boreq/vivarium/vivarium_assistant/src/domain/outputs.rs

use super::{InputPin, OutputPin, OutputPinState, PinNumber, GPIO};
use crate::errors::Result;
use anyhow::anyhow;
use chrono::TimeDelta;
use chrono::{DateTime, Local, NaiveTime, Utc};
use log::info;
use std::fmt::Display;
use std::time::Duration;

pub trait CurrentTimeProvider {
    fn now(&self) -> DateTime<Utc>;
}

#[derive(Copy, Debug, Clone, PartialEq)]
pub struct ScheduledActivation {
    when: NaiveTime,
    for_seconds: u32,
}

impl ScheduledActivation {
    const SECONDS_IN_AN_IMAGINARY_DAY: u32 = 24 * 60 * 60;

    pub fn new(when: NaiveTime, for_seconds: u32) -> Result<Self> {
        if for_seconds == 0 {
            return Err(anyhow!("activating for 0 seconds is nonsense"));
        }

        if for_seconds > ScheduledActivation::SECONDS_IN_AN_IMAGINARY_DAY {
            return Err(anyhow!(format!(
                "since this type effectively represents durations on an imaginary clock face this
                time the day really is up to {} seconds long and it isn't just the programmer's
                delusion; the provided for_seconds exceeds that",
                ScheduledActivation::SECONDS_IN_AN_IMAGINARY_DAY
            )));
        }

        Ok(Self { when, for_seconds })
    }

    pub fn overlaps(&self, other: &Self) -> bool {
        if self.has_inside(&other.when) {
            return true;
        }
        if self.has_inside(&other.end()) {
            return true;
        }
        if other.has_inside(&self.end()) {
            return true;
        }

        false
    }

    pub fn has_inside(&self, time: &NaiveTime) -> bool {
        let start = self.when;
        let end = self.end();

        if start == end {
            return true;
        }

        let jumps_over_midnight = end < start;
        if jumps_over_midnight {
            time >= &start || time <= &end
        } else {
            time >= &start && time <= &end
        }
    }

    pub fn repeat(&self, start_every_seconds: u32, times: u32) -> Result<Vec<ScheduledActivation>> {
        if start_every_seconds == 0 {
            return Err(anyhow!("repeating every zero seconds makes no sense"));
        }

        if start_every_seconds <= self.for_seconds {
            return Err(anyhow!("repeating more often than or just as often as for_seconds makes no sense, the results will overlap"));
        }

        if times <= 1 {
            return Err(anyhow!(
                "repeating less than two times makes no sense, just use the existing activation"
            ));
        }

        let mut result = vec![];
        let start_every = Duration::from_secs(start_every_seconds.into());
        for i in 0..times {
            let jump = start_every * i;
            if jump.as_secs() >= ScheduledActivation::SECONDS_IN_AN_IMAGINARY_DAY.into() {
                return Err(anyhow!(
                    "there is no way we meant to jump by more than a whole day or a whole day when repeating"
                ));
            }
            let when = self.when + jump;
            let when_jumps_over_midnight = when < self.when;
            if when_jumps_over_midnight {
                return Err(anyhow!(
                    "I find it highly suspicious that we jumped over midnight when repeating, I suspect we didn't want this to happen"
                ));
            }

            let activation = ScheduledActivation::new(when, self.for_seconds)?;
            result.push(activation);
        }
        Ok(result)
    }

    fn end(&self) -> NaiveTime {
        self.when + TimeDelta::seconds(self.for_seconds as i64)
    }
}

#[derive(Debug, Clone, PartialEq)]
pub struct ScheduledActivations {
    activations: Vec<ScheduledActivation>,
}

impl ScheduledActivations {
    pub fn new(activations: &[ScheduledActivation]) -> Result<Self> {
        let mut v = vec![];
        for (i, a) in activations.iter().enumerate() {
            for (j, b) in activations.iter().enumerate() {
                if i != j && a.overlaps(b) {
                    return Err(anyhow!("activations can't overlap"));
                }
            }
            v.push(*a);
        }

        Ok(ScheduledActivations { activations: v })
    }

    pub fn has_inside(&self, time: &NaiveTime) -> bool {
        for activation in &self.activations {
            if activation.has_inside(time) {
                return true;
            }
        }
        false
    }
}

#[derive(Debug, Clone, Hash, Eq, PartialEq)]
pub struct OutputName {
    name: String,
}

impl OutputName {
    pub fn new(name: impl Into<String>) -> Result<Self> {
        let name = name.into();
        if name.is_empty() {
            return Err(anyhow!("output name can't be empty"));
        }
        Ok(Self { name })
    }

    pub fn name(&self) -> &str {
        &self.name
    }
}

impl Display for OutputName {
    fn fmt(&self, f: &mut std::fmt::Formatter<'_>) -> std::fmt::Result {
        write!(f, "{}", self.name)
    }
}

#[derive(Debug, Clone, PartialEq)]
pub struct OutputDefinition {
    name: OutputName,
    pin: PinNumber,
    activations: ScheduledActivations,
}

impl OutputDefinition {
    pub fn new(name: OutputName, pin: PinNumber, activations: ScheduledActivations) -> Self {
        Self {
            name,
            pin,
            activations,
        }
    }
}

#[derive(Debug, Clone, PartialEq)]
pub struct OutputDefinitions {
    outputs: Vec<OutputDefinition>,
}

impl OutputDefinitions {
    pub fn new(outputs: &[OutputDefinition]) -> Result<Self> {
        let mut v = vec![];
        for (i, a) in outputs.iter().enumerate() {
            for (j, b) in outputs.iter().enumerate() {
                if i == j {
                    continue;
                }

                if a.name == b.name {
                    return Err(anyhow!("identical output names"));
                }

                if a.pin == b.pin {
                    return Err(anyhow!("duplicate pin numbers"));
                }
            }
            v.push(a.clone());
        }

        Ok(Self { outputs: v })
    }

    pub fn outputs(&self) -> &[OutputDefinition] {
        &self.outputs
    }
}

pub struct Controller<OP: OutputPin, CTP: CurrentTimeProvider> {
    outputs: Vec<ControlledOutput<OP>>,
    current_time_provider: CTP,
}

impl<OP: OutputPin, CTP: CurrentTimeProvider> Controller<OP, CTP> {
    pub fn new<IP: InputPin, GP: GPIO<OP, IP>>(
        outputs: &OutputDefinitions,
        gpio: GP,
        current_time_provider: CTP,
    ) -> Result<Controller<OP, CTP>> {
        let outputs_with_pin: Result<Vec<ControlledOutput<OP>>> = outputs
            .outputs()
            .iter()
            .map(|v| {
                Ok(ControlledOutput {
                    definition: v.clone(),
                    overrides: vec![],
                    pin: gpio.output(&v.pin)?,
                })
            })
            .collect();

        Ok(Controller {
            outputs: outputs_with_pin?,
            current_time_provider,
        })
    }

    pub fn update_outputs(&mut self) {
        let now = self.current_time_provider.now();
        self.update_outputs_for_time(now.into());
    }

    fn update_outputs_for_time(&mut self, now: DateTime<Local>) {
        for output in &mut self.outputs {
            match output.target_state(&now.time()) {
                OutputState::On => {
                    if output.pin.state() != OutputPinState::High {
                        info!("turning on output '{name}'", name = output.definition.name);
                        output.pin.set_high();
                    }
                }
                OutputState::Off => {
                    if output.pin.state() != OutputPinState::Low {
                        info!("turning off output '{name}'", name = output.definition.name);
                        output.pin.set_low();
                    }
                }
            }

            output.cleanup_overrides(&now.time());
        }
    }

    pub fn add_override(
        &mut self,
        output_name: OutputName,
        state: OutputState,
        activation: ScheduledActivation,
    ) -> Result<()> {
        for output in &mut self.outputs {
            if output.definition.name == output_name {
                info!(
                    "adding override to state {state} for output '{name}' starting at {when} and lasting {for_seconds} seconds",
                    state = state,
                    name = output_name,
                    when  = activation.when,
                    for_seconds =activation.for_seconds
                );
                output.overrides.push(Override::new(state, activation));
                return Ok(());
            }
        }

        Err(anyhow!("output {:?} doesn't exist", output_name))
    }

    pub fn clear_overrides(&mut self, output_name: OutputName) -> Result<()> {
        for output in &mut self.outputs {
            if output.definition.name == output_name {
                output.overrides.clear();
                return Ok(());
            }
        }

        Err(anyhow!("output {:?} doesn't exist", output_name))
    }

    pub fn fail_safe(&mut self) {
        for output in &mut self.outputs {
            output.pin.set_low();
        }
    }

    pub fn status(&self) -> Vec<OutputStatus> {
        let mut result = vec![];
        for output in &self.outputs {
            let status = OutputStatus {
                name: output.definition.name.clone(),
                state: output.pin.state().into(),
            };
            result.push(status);
        }
        result
    }
}

pub struct OutputStatus {
    pub name: OutputName,
    pub state: OutputState,
}

#[derive(Debug, Clone, Copy, PartialEq)]
pub enum OutputState {
    On,
    Off,
}

impl From<OutputPinState> for OutputState {
    fn from(value: OutputPinState) -> Self {
        match value {
            OutputPinState::Low => Self::Off,
            OutputPinState::High => Self::On,
        }
    }
}

impl Display for OutputState {
    fn fmt(&self, f: &mut std::fmt::Formatter<'_>) -> std::fmt::Result {
        match self {
            OutputState::On => write!(f, "on"),
            OutputState::Off => write!(f, "off"),
        }
    }
}

#[derive(Debug, Clone, PartialEq)]
struct Override {
    state: OutputState,
    activation: ScheduledActivation,
    was_triggered: bool,
}

impl Override {
    fn new(state: OutputState, activation: ScheduledActivation) -> Self {
        Self {
            state,
            activation,
            was_triggered: false,
        }
    }
}

struct ControlledOutput<OP: OutputPin> {
    definition: OutputDefinition,
    pin: OP,
    overrides: Vec<Override>,
}

impl<OP: OutputPin> ControlledOutput<OP> {
    fn target_state(&mut self, now: &NaiveTime) -> OutputState {
        for o in &mut self.overrides {
            if o.activation.has_inside(now) {
                o.was_triggered = true;
                return o.state;
            }
        }

        if self.definition.activations.has_inside(now) {
            OutputState::On
        } else {
            OutputState::Off
        }
    }

    fn cleanup_overrides(&mut self, now: &NaiveTime) {
        self.overrides
            .retain(|v| v.activation.has_inside(now) || !v.was_triggered);
    }
}

#[cfg(test)]
mod tests {
    use super::*;

    #[cfg(test)]
    mod scheduled_activation {
        use std::panic;

        use super::*;

        #[test]
        fn test_has_inside() -> Result<()> {
            struct TestCase<'a> {
                name: &'a str,
                activation: ScheduledActivation,
                time: NaiveTime,
                expected_has_inside: bool,
            }

            let test_cases = vec![
                TestCase {
                    name: "midnight_start",
                    activation: ScheduledActivation::new(new_time(23, 59, 55), 10)?,
                    time: new_time(23, 59, 55),
                    expected_has_inside: true,
                },
                TestCase {
                    name: "midnight_middle_before",
                    activation: ScheduledActivation::new(new_time(23, 59, 55), 10)?,
                    time: new_time(23, 59, 59),
                    expected_has_inside: true,
                },
                TestCase {
                    name: "midnight_middle_after",
                    activation: ScheduledActivation::new(new_time(23, 59, 55), 10)?,
                    time: new_time(00, 00, 00),
                    expected_has_inside: true,
                },
                TestCase {
                    name: "midnight_end",
                    activation: ScheduledActivation::new(new_time(23, 59, 55), 10)?,
                    time: new_time(00, 00, 5),
                    expected_has_inside: true,
                },
                TestCase {
                    name: "midnight_outside",
                    activation: ScheduledActivation::new(new_time(23, 59, 55), 10)?,
                    time: new_time(12, 00, 00),
                    expected_has_inside: false,
                },
                TestCase {
                    name: "normal_start",
                    activation: ScheduledActivation::new(new_time(12, 0, 0), 10)?,
                    time: new_time(12, 0, 0),
                    expected_has_inside: true,
                },
                TestCase {
                    name: "normal_middle",
                    activation: ScheduledActivation::new(new_time(12, 0, 0), 10)?,
                    time: new_time(12, 0, 5),
                    expected_has_inside: true,
                },
                TestCase {
                    name: "normal_end",
                    activation: ScheduledActivation::new(new_time(12, 0, 0), 10)?,
                    time: new_time(12, 0, 10),
                    expected_has_inside: true,
                },
                TestCase {
                    name: "normal_outside",
                    activation: ScheduledActivation::new(new_time(12, 0, 0), 10)?,
                    time: new_time(18, 0, 0),
                    expected_has_inside: false,
                },
                TestCase {
                    name: "always_turned_on",
                    activation: ScheduledActivation::new(new_time(0, 0, 0), 24 * 3600)?,
                    time: new_time(1, 0, 0),
                    expected_has_inside: true,
                },
            ];

            for test_case in &test_cases {
                println!("test case: {}", test_case.name);
                assert_eq!(
                    test_case.activation.has_inside(&test_case.time),
                    test_case.expected_has_inside
                );
            }

            Ok(())
        }

        #[test]
        fn test_overlaps() -> Result<()> {
            struct TestCase<'a> {
                name: &'a str,
                a: ScheduledActivation,
                b: ScheduledActivation,
                expected_overlaps: bool,
            }

            let test_cases = vec![
                TestCase {
                    name: "identical",
                    a: ScheduledActivation::new(new_time(14, 0, 0), 10)?,
                    b: ScheduledActivation::new(new_time(14, 0, 0), 10)?,
                    expected_overlaps: true,
                },
                TestCase {
                    name: "inside",
                    a: ScheduledActivation::new(new_time(14, 0, 0), 20)?,
                    b: ScheduledActivation::new(new_time(14, 0, 5), 10)?,
                    expected_overlaps: true,
                },
                TestCase {
                    name: "overlap",
                    a: ScheduledActivation::new(new_time(14, 0, 0), 10)?,
                    b: ScheduledActivation::new(new_time(14, 0, 5), 10)?,
                    expected_overlaps: true,
                },
                TestCase {
                    name: "outside",
                    a: ScheduledActivation::new(new_time(14, 0, 0), 10)?,
                    b: ScheduledActivation::new(new_time(18, 0, 0), 10)?,
                    expected_overlaps: false,
                },
                TestCase {
                    name: "midnight_inside",
                    a: ScheduledActivation::new(new_time(23, 59, 50), 20)?,
                    b: ScheduledActivation::new(new_time(23, 59, 55), 10)?,
                    expected_overlaps: true,
                },
                TestCase {
                    name: "midnight_inside_before",
                    a: ScheduledActivation::new(new_time(23, 59, 50), 20)?,
                    b: ScheduledActivation::new(new_time(23, 59, 55), 1)?,
                    expected_overlaps: true,
                },
                TestCase {
                    name: "midnight_inside_after",
                    a: ScheduledActivation::new(new_time(23, 59, 50), 20)?,
                    b: ScheduledActivation::new(new_time(00, 0, 5), 1)?,
                    expected_overlaps: true,
                },
                TestCase {
                    name: "midnight_outside",
                    a: ScheduledActivation::new(new_time(23, 59, 50), 20)?,
                    b: ScheduledActivation::new(new_time(18, 0, 0), 10)?,
                    expected_overlaps: false,
                },
            ];

            for test_case in &test_cases {
                println!("test case: {}", test_case.name);

                assert_eq!(
                    test_case.a.overlaps(&test_case.b),
                    test_case.expected_overlaps
                );

                assert_eq!(
                    test_case.b.overlaps(&test_case.a),
                    test_case.expected_overlaps
                );
            }

            Ok(())
        }

        #[test]
        fn test_repeat() -> Result<()> {
            struct TestCase<'a> {
                name: &'a str,
                activation: ScheduledActivation,
                start_every: u32,
                times: u32,
                result: Result<Vec<ScheduledActivation>>,
            }

            let test_cases = vec![
                TestCase {
                name: "zero_times",
                activation: ScheduledActivation::new(new_time(14, 0, 0), 10)?,
                start_every: 15,
                times: 0,
                result: Err(anyhow!("repeating less than two times makes no sense, just use the existing activation")),
            },
                TestCase {
                name: "one_time",
                activation: ScheduledActivation::new(new_time(14, 0, 0), 10)?,
                start_every: 15,
                times: 1,
                result: Err(anyhow!("repeating less than two times makes no sense, just use the existing activation")),
            },
                TestCase {
                name: "just_as_often",
                activation: ScheduledActivation::new(new_time(14, 0, 0), 10)?,
                start_every: 10,
                times: 2,
                result: Err(anyhow!("repeating more often than or just as often as for_seconds makes no sense, the results will overlap")),
            },
                TestCase {
                name: "more_often",
                activation: ScheduledActivation::new(new_time(14, 0, 0), 10)?,
                start_every: 9,
                times: 2,
                result: Err(anyhow!("repeating more often than or just as often as for_seconds makes no sense, the results will overlap")),
            },
                TestCase {
                name: "simple",
                activation: ScheduledActivation::new(new_time(14, 0, 0), 10)?,
                start_every: 15,
                times: 2,
                result: Ok(vec![
                    ScheduledActivation::new(new_time(14, 0, 0), 10)?,
                    ScheduledActivation::new(new_time(14, 0, 15), 10)?,
                ]),
            },
            TestCase {
                name: "start_every_longer_than_a_day",
                activation: ScheduledActivation::new(new_time(14, 0, 0), 10)?,
                start_every: 25 * 60 * 60,
                times: 2,
                result: Err(anyhow!("there is no way we meant to jump by more than a whole day or a whole day when repeating")),
            },
            TestCase {
                name: "start_every_equal_to_one_day",
                activation: ScheduledActivation::new(new_time(14, 0, 0), 10)?,
                start_every: 24 * 60 * 60,
                times: 2,
                result: Err(anyhow!("there is no way we meant to jump by more than a whole day or a whole day when repeating")),
            },
            TestCase {
                name: "start_jumps_over_midnight",
                activation: ScheduledActivation::new(new_time(23, 0, 0), 60)?,
                start_every: 60 * 60,
                times: 2,
                result: Err(anyhow!("I find it highly suspicious that we jumped over midnight when repeating, I suspect we didn't want this to happen")),
            },
            ];

            for test_case in &test_cases {
                println!("test case: {}", test_case.name);

                let result = test_case
                    .activation
                    .repeat(test_case.start_every, test_case.times);
                match &test_case.result {
                    Ok(a) => match result {
                        Ok(b) => assert_eq!(a, &b),
                        Err(err_b) => panic!("got an error when a value was expected: {:?}", err_b),
                    },
                    Err(err_a) => match result {
                        Ok(b) => panic!("got a value when an error was expected: {:?}", b),
                        Err(err_b) => assert_eq!(err_a.to_string(), err_b.to_string()),
                    },
                }
            }

            Ok(())
        }
    }

    mod scheduled_activations {
        use super::*;
        use anyhow::Error;
        use core::panic;

        #[test]
        fn test_construct() -> Result<()> {
            struct TestCase<'a> {
                name: &'a str,
                activations: Vec<ScheduledActivation>,
                expected_error: Option<Error>,
            }

            let test_cases = vec![
                TestCase {
                    name: "empty",
                    activations: vec![],
                    expected_error: None,
                },
                TestCase {
                    name: "overlap",
                    activations: vec![
                        ScheduledActivation::new(new_time(12, 0, 0), 10)?,
                        ScheduledActivation::new(new_time(12, 0, 5), 10)?,
                    ],
                    expected_error: Some(anyhow!("activations can't overlap")),
                },
                TestCase {
                    name: "ok",
                    activations: vec![
                        ScheduledActivation::new(new_time(12, 0, 0), 10)?,
                        ScheduledActivation::new(new_time(18, 0, 0), 10)?,
                    ],
                    expected_error: None,
                },
            ];

            for test_case in &test_cases {
                println!("test case: {}", test_case.name);

                let result = ScheduledActivations::new(&test_case.activations);
                match &test_case.expected_error {
                    Some(expected_err) => match result {
                        Ok(_) => {
                            panic!("no error encountered even though an error was expected")
                        }
                        Err(err) => {
                            assert_eq!(err.to_string(), expected_err.to_string());
                        }
                    },
                    None => {
                        match result {
                            Ok(_) => {
                                // ok
                            }
                            Err(_) => {
                                panic!("error encountered even though no error was expected")
                            }
                        }
                    }
                }
            }

            Ok(())
        }
    }

    mod controlled_output {
        use super::*;
        use crate::adapters::MockOutputPin;

        #[test]
        fn test_target_state() -> Result<()> {
            struct TestCase<'a> {
                name: &'a str,
                activations: Vec<ScheduledActivation>,
                overrides: Vec<Override>,
                expected_state: OutputState,
            }

            let time = new_time(12, 00, 00);
            let test_cases = vec![
                TestCase {
                    name: "empty",
                    activations: vec![],
                    overrides: vec![],
                    expected_state: OutputState::Off,
                },
                TestCase {
                    name: "no_override",
                    activations: vec![ScheduledActivation::new(new_time(11, 59, 55), 10)?],
                    overrides: vec![],
                    expected_state: OutputState::On,
                },
                TestCase {
                    name: "override_off",
                    activations: vec![ScheduledActivation::new(new_time(11, 59, 55), 10)?],
                    overrides: vec![Override::new(
                        OutputState::Off,
                        ScheduledActivation::new(new_time(11, 59, 55), 10)?,
                    )],
                    expected_state: OutputState::Off,
                },
                TestCase {
                    name: "override_on",
                    activations: vec![ScheduledActivation::new(new_time(18, 00, 00), 10)?],
                    overrides: vec![Override::new(
                        OutputState::On,
                        ScheduledActivation::new(new_time(11, 59, 55), 10)?,
                    )],
                    expected_state: OutputState::On,
                },
            ];

            for test_case in &test_cases {
                println!("test case: {}", test_case.name);

                let pin_number = PinNumber::new(1)?;
                let activations = ScheduledActivations::new(&test_case.activations)?;
                let definition =
                    OutputDefinition::new(OutputName::new("output")?, pin_number, activations);
                let mut output = ControlledOutput {
                    definition,
                    pin: MockOutputPin::new(pin_number),
                    overrides: test_case.overrides.clone(),
                };

                let result = output.target_state(&time);
                assert_eq!(result, test_case.expected_state);
            }

            Ok(())
        }

        #[test]
        fn test_cleanup_overrides() -> Result<()> {
            struct TestCase<'a> {
                name: &'a str,
                overrides: Vec<Override>,
                expected_overrides: Vec<Override>,
            }

            let time = new_time(12, 00, 00);
            let test_cases = vec![
                TestCase {
                    name: "future_override",
                    overrides: vec![Override {
                        state: OutputState::On,
                        activation: ScheduledActivation::new(new_time(18, 00, 00), 10)?,
                        was_triggered: false,
                    }],
                    expected_overrides: vec![Override {
                        state: OutputState::On,
                        activation: ScheduledActivation::new(new_time(18, 00, 00), 10)?,
                        was_triggered: false,
                    }],
                },
                TestCase {
                    name: "past_override",
                    overrides: vec![
                        Override {
                            state: OutputState::On,
                            activation: ScheduledActivation::new(new_time(18, 00, 00), 10)?,
                            was_triggered: false,
                        },
                        Override {
                            state: OutputState::On,
                            activation: ScheduledActivation::new(new_time(6, 00, 00), 10)?,
                            was_triggered: true,
                        },
                    ],
                    expected_overrides: vec![Override {
                        state: OutputState::On,
                        activation: ScheduledActivation::new(new_time(18, 00, 00), 10)?,
                        was_triggered: false,
                    }],
                },
                TestCase {
                    name: "current_override",
                    overrides: vec![
                        Override {
                            state: OutputState::On,
                            activation: ScheduledActivation::new(new_time(18, 00, 00), 10)?,
                            was_triggered: false,
                        },
                        Override {
                            state: OutputState::On,
                            activation: ScheduledActivation::new(new_time(11, 59, 55), 10)?,
                            was_triggered: true,
                        },
                    ],
                    expected_overrides: vec![
                        Override {
                            state: OutputState::On,
                            activation: ScheduledActivation::new(new_time(18, 00, 00), 10)?,
                            was_triggered: false,
                        },
                        Override {
                            state: OutputState::On,
                            activation: ScheduledActivation::new(new_time(11, 59, 55), 10)?,
                            was_triggered: true,
                        },
                    ],
                },
            ];

            for test_case in &test_cases {
                println!("test case: {}", test_case.name);

                let pin_number = PinNumber::new(1)?;
                let activations = ScheduledActivations::new(&[])?;
                let definition =
                    OutputDefinition::new(OutputName::new("output")?, pin_number, activations);
                let mut output = ControlledOutput {
                    definition,
                    pin: MockOutputPin::new(pin_number),
                    overrides: test_case.overrides.clone(),
                };

                output.cleanup_overrides(&time);
                assert_eq!(output.overrides, test_case.expected_overrides);
            }

            Ok(())
        }
    }

    pub fn new_time(hour: u32, min: u32, sec: u32) -> NaiveTime {
        NaiveTime::from_hms_opt(hour, min, sec).expect("from_hms_opt")
    }
}
